ilkarataev/esphome_BRM/4_relays_modules/images/Box1.jpg

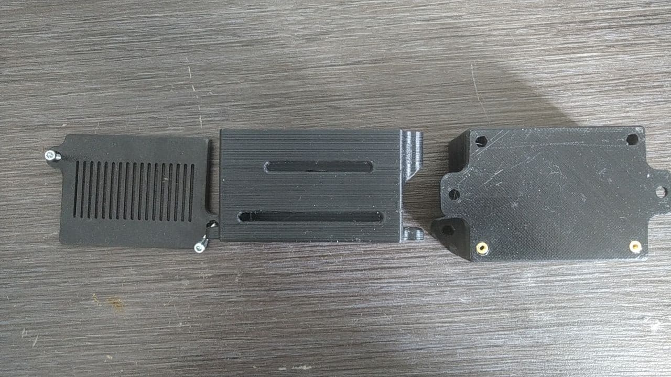
4_relays_modules/images/Box1.jpg
