ilkarataev/esphome_BRM/4_relays_modules/images/Box.jpg

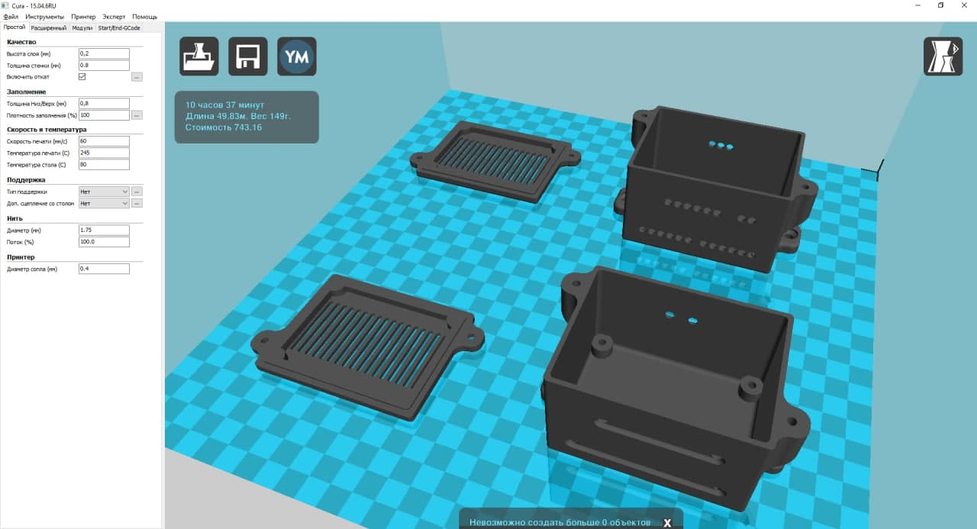
4_relays_modules/images/Box.jpg
