ilkarataev/esphome_BRM/8_relays_modules/images/install.jpg

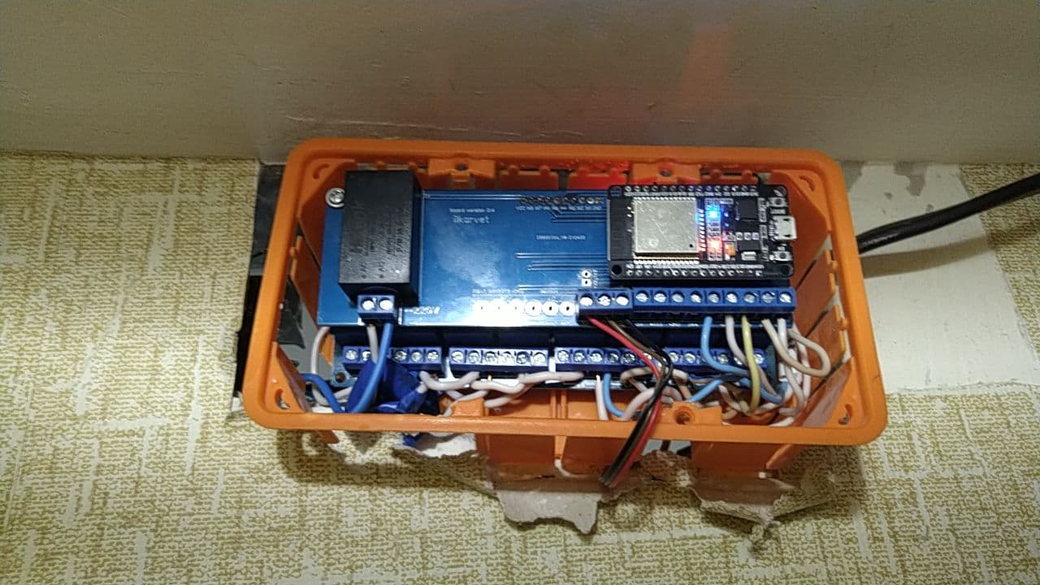
8_relays_modules/images/install.jpg
