ilkarataev/esphome_BRM/8_relays_modules/images/prototype_fabrication2.jpg

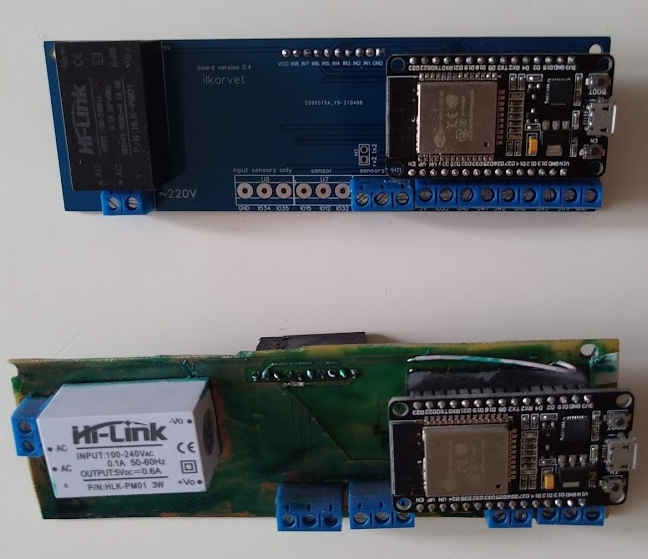
8_relays_modules/images/prototype_fabrication2.jpg
